KaiGaertner/citypolls/website/images/try-p-500.png

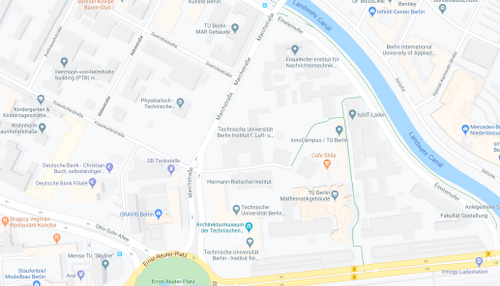
website/images/try-p-500.png
